ssashton/cyrus-pre-volume/Cyrus Pre Audio Measurments/Cyrus Pre Volume Original.png

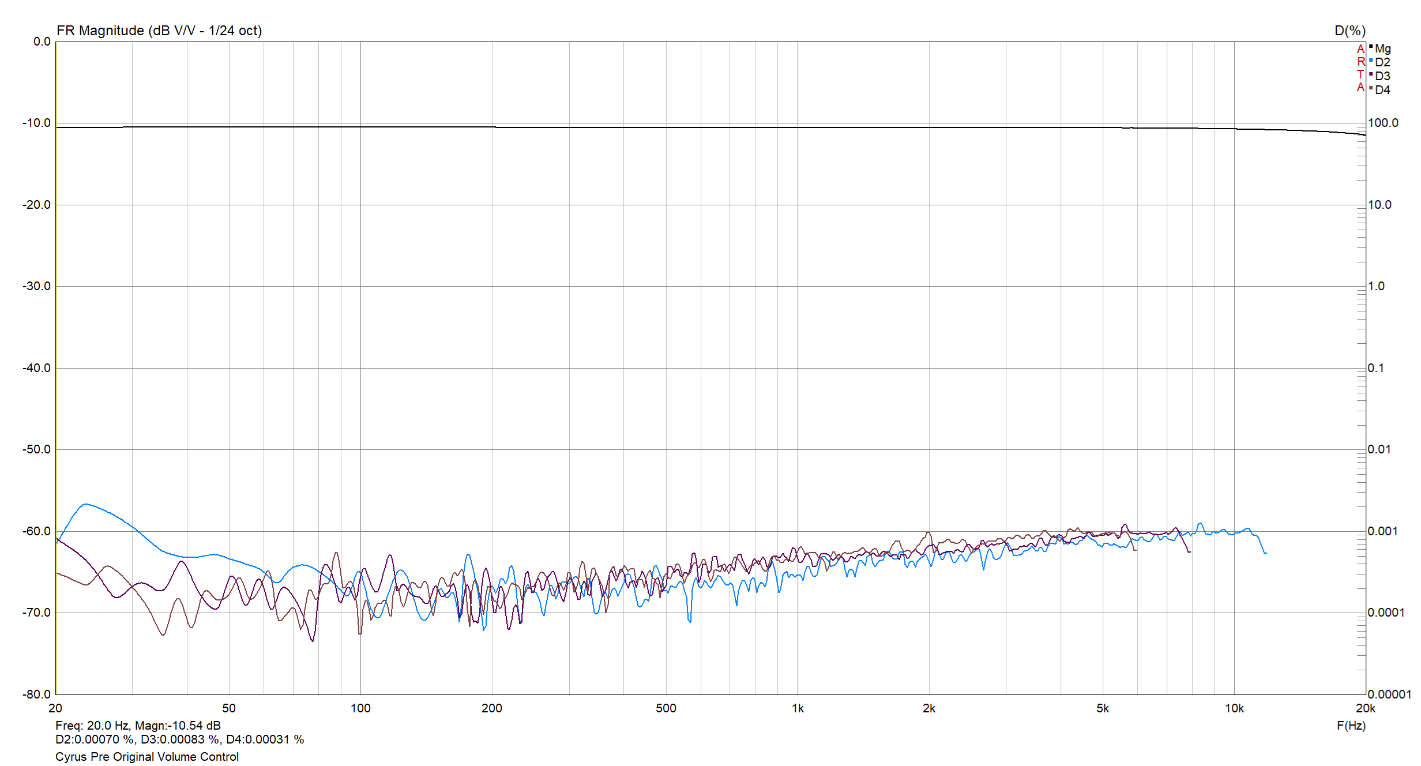
Cyrus Pre Audio Measurments/Cyrus Pre Volume Original.png
