ssashton/cyrus-pre-volume/Cyrus Pre Images/0fe24d15-2bc2-4b44-9fb7-35bb59eaa051.jpg

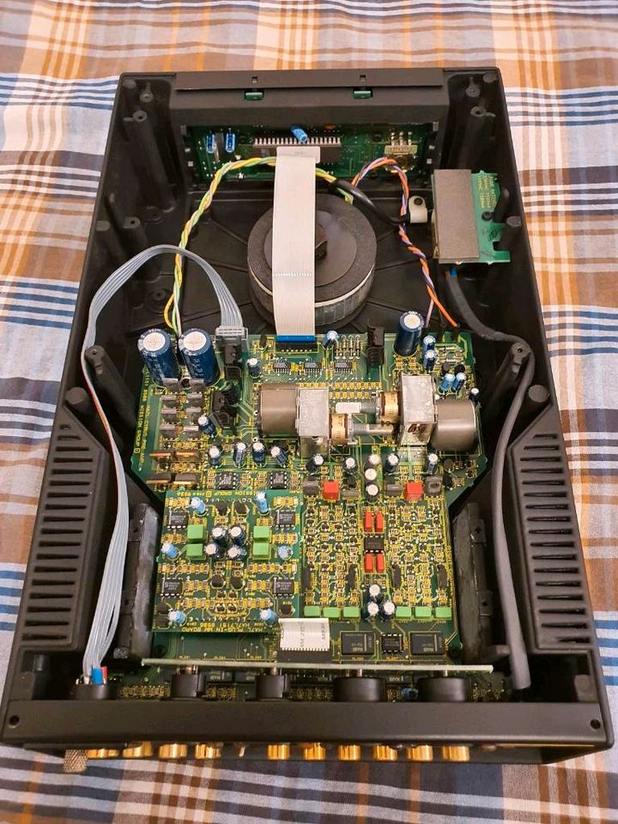
Cyrus Pre Images/0fe24d15-2bc2-4b44-9fb7-35bb59eaa051.jpg
