ssashton/cyrus-pre-volume/Cyrus Pre Images/20250813_225020.jpg

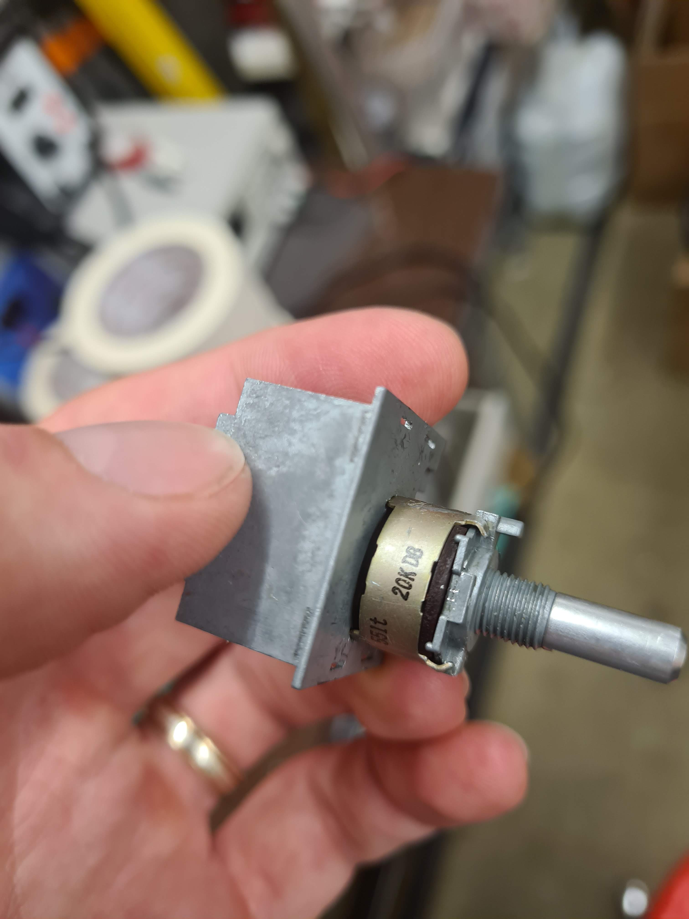
Cyrus Pre Images/20250813_225020.jpg
