ssashton/cyrus-pre-volume/Cyrus Pre Images/20250813_225022.jpg

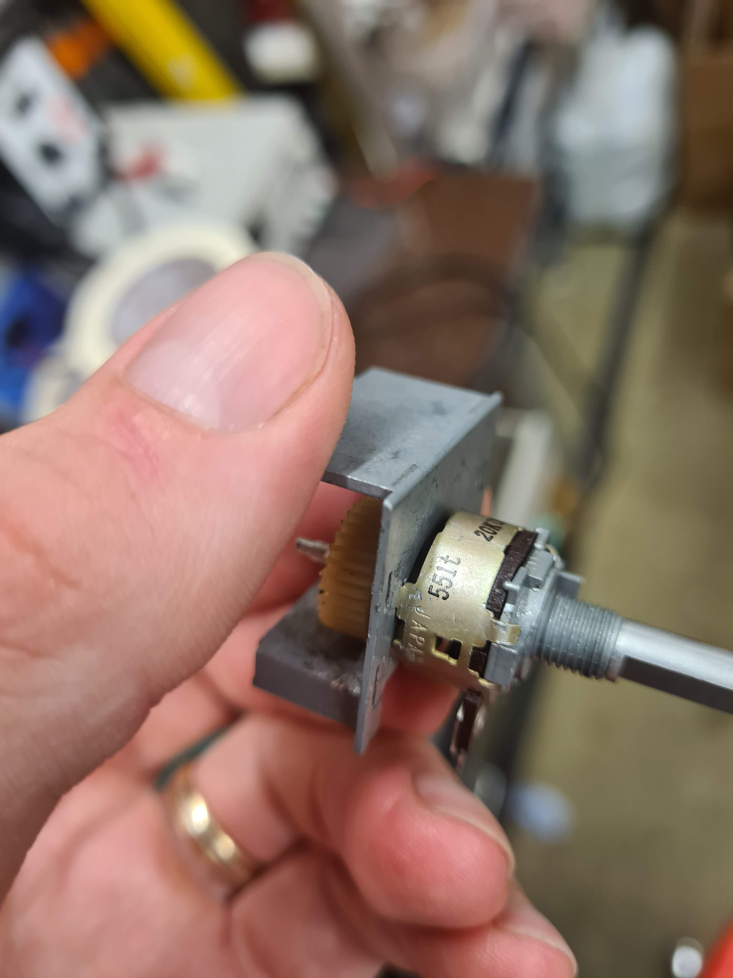
Cyrus Pre Images/20250813_225022.jpg
