ssashton/cyrus-pre-volume/Cyrus Pre Images/20251005_141955.jpg

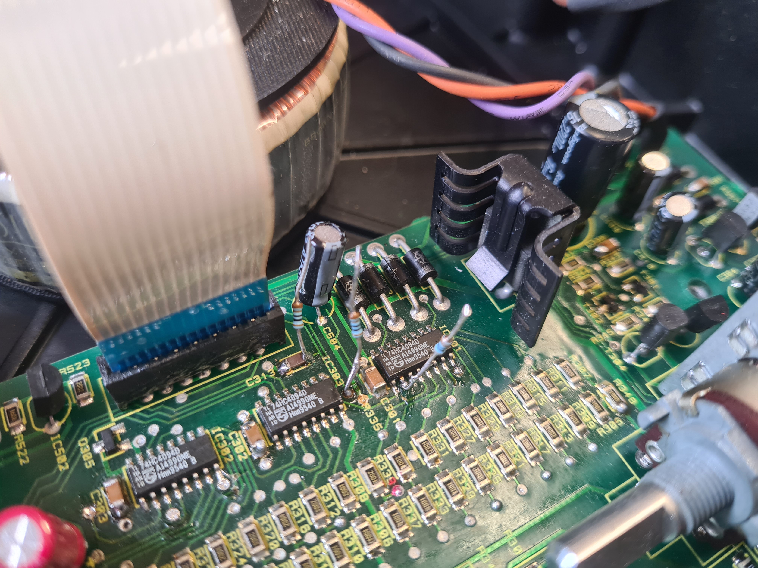
Cyrus Pre Images/20251005_141955.jpg
