ssashton/cyrus-pre-volume/Cyrus Pre Images/20251005_143241.jpg

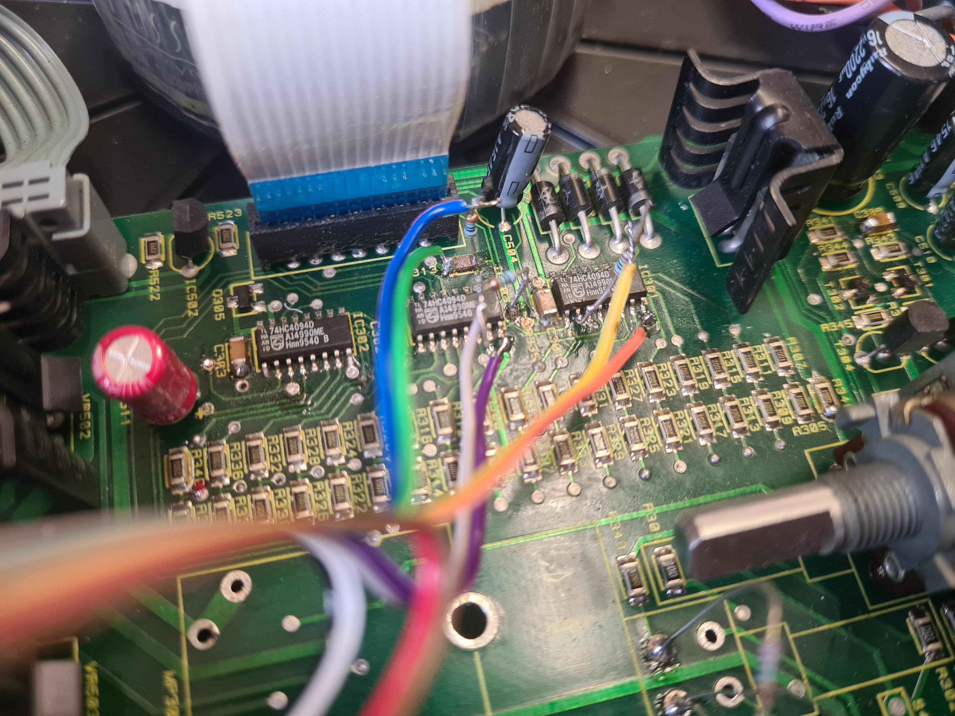
Cyrus Pre Images/20251005_143241.jpg
