ssashton/cyrus-pre-volume/Cyrus Pre Images/20251005_143256.jpg

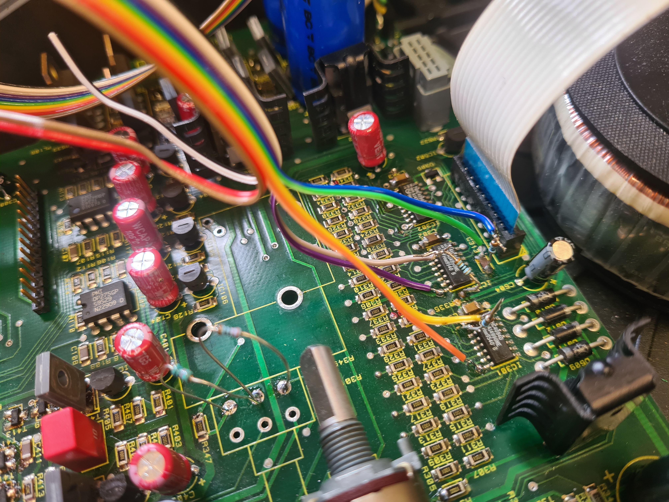
Cyrus Pre Images/20251005_143256.jpg
