ssashton/cyrus-pre-volume/Cyrus Pre Images/20251109_150557.jpg

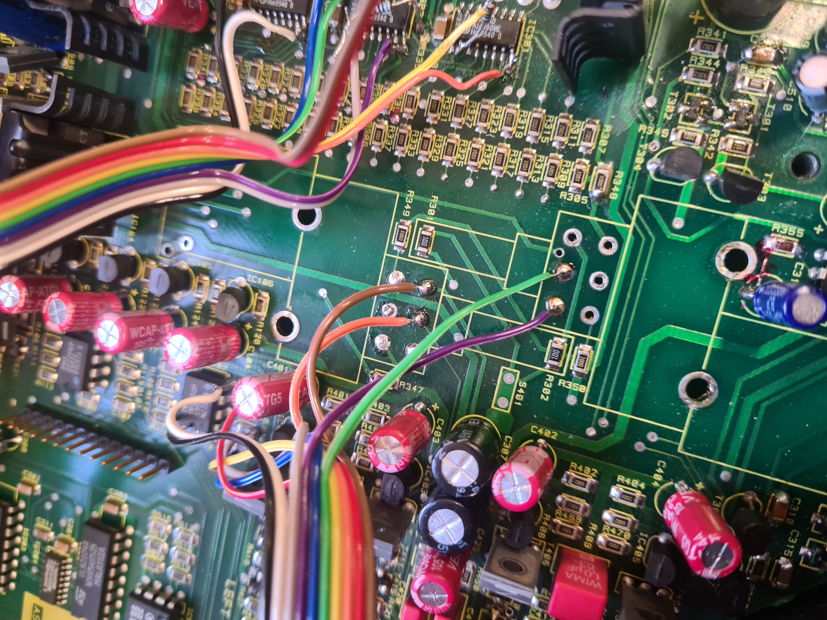
Cyrus Pre Images/20251109_150557.jpg
