ssashton/cyrus-pre-volume/Cyrus Pre Images/20251109_150601.jpg

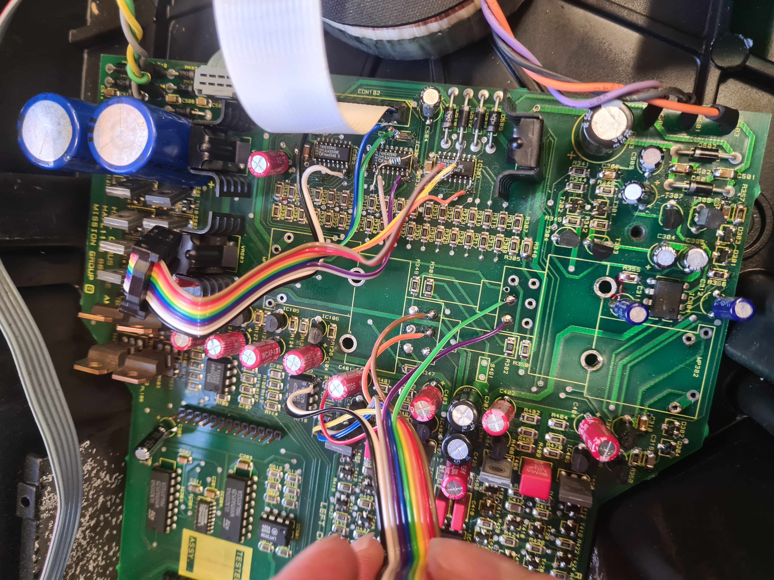
Cyrus Pre Images/20251109_150601.jpg
