ssashton/cyrus-pre-volume/Cyrus Pre Images/20251109_150613.jpg

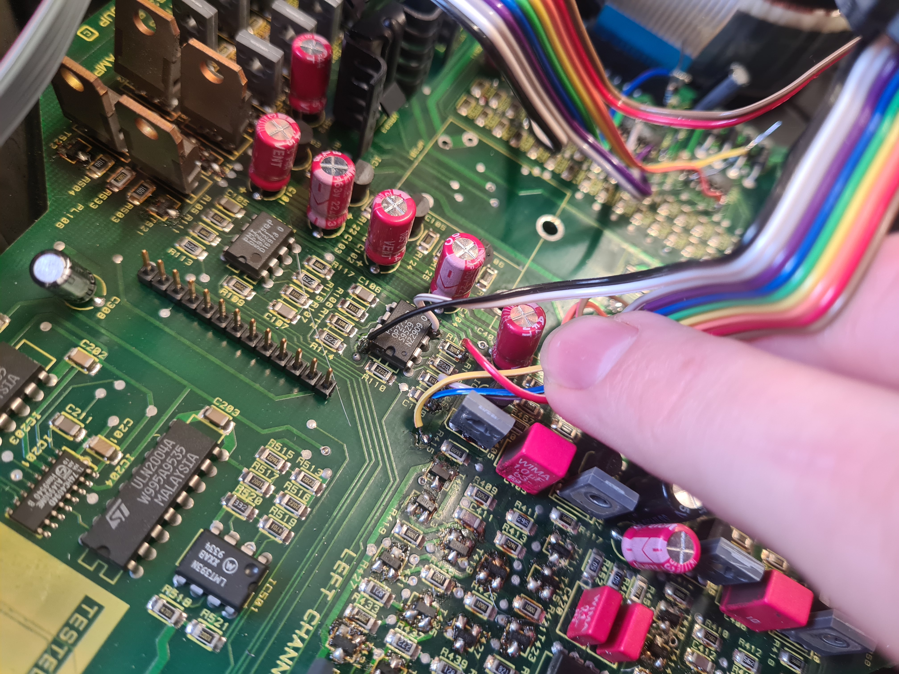
Cyrus Pre Images/20251109_150613.jpg
