ssashton/cyrus-pre-volume/Cyrus Pre Images/c8a0d77d-515b-400d-b8cd-d2a9fd72f0e5.jpg

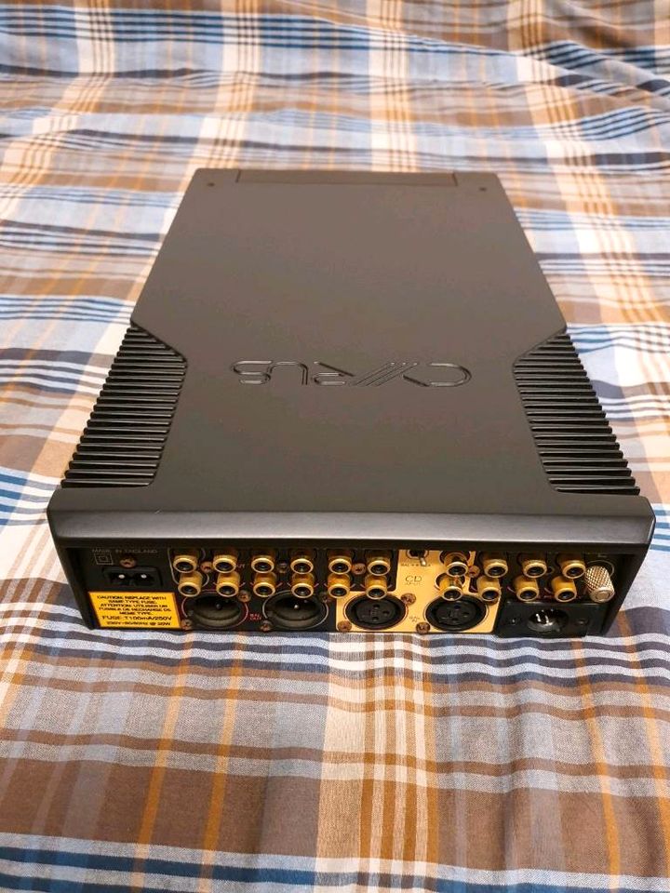
Cyrus Pre Images/c8a0d77d-515b-400d-b8cd-d2a9fd72f0e5.jpg
