ssashton/cyrus-pre-volume/Cyrus Pre Images/mission_pre_pot.jpg

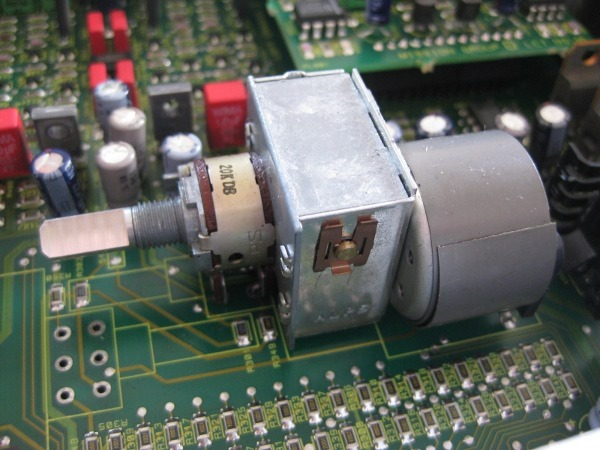
Cyrus Pre Images/mission_pre_pot.jpg
