ssashton/cyrus-pre-volume/Cyrus Pre Images/20251005_141931.jpg

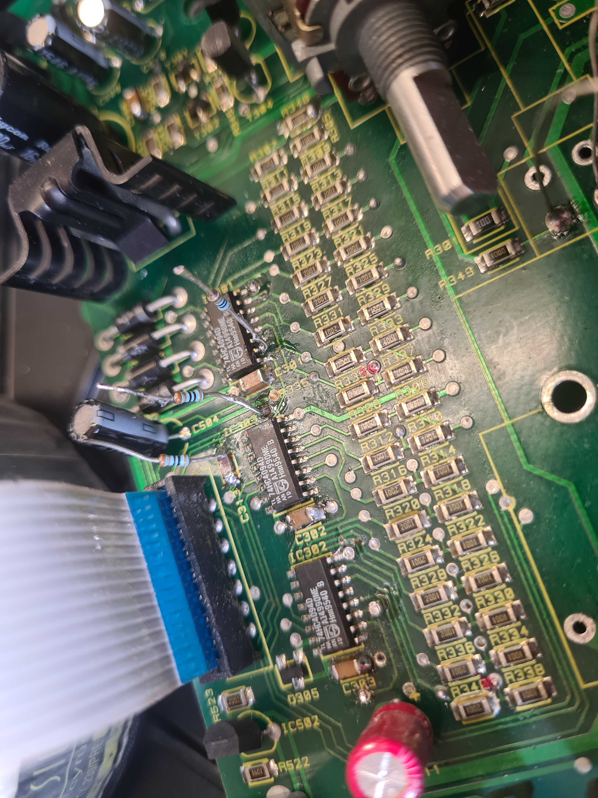
Cyrus Pre Images/20251005_141931.jpg
