ssashton/cyrus-pre-volume/Cyrus Pre Images/20251006_142524.jpg

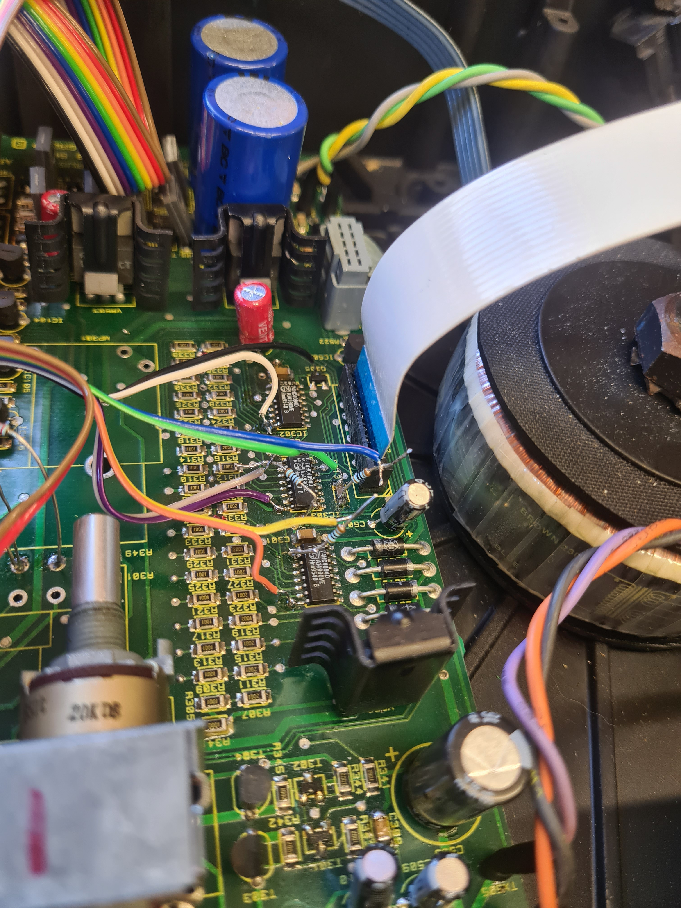
Cyrus Pre Images/20251006_142524.jpg
