ssashton/cyrus-pre-volume/Cyrus Pre Images/20251109_151317.jpg

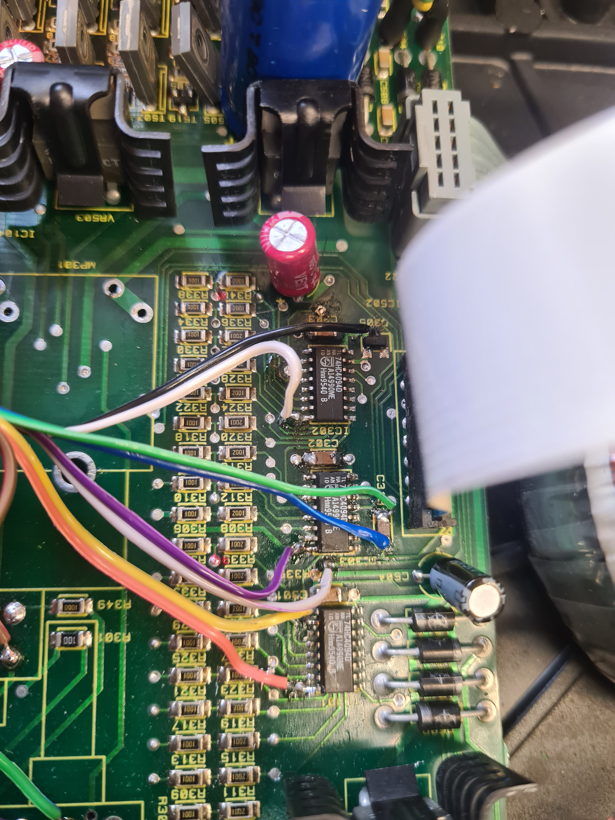
Cyrus Pre Images/20251109_151317.jpg
