ssashton/cyrus-pre-volume/Cyrus Pre Images/20251109_151350.jpg

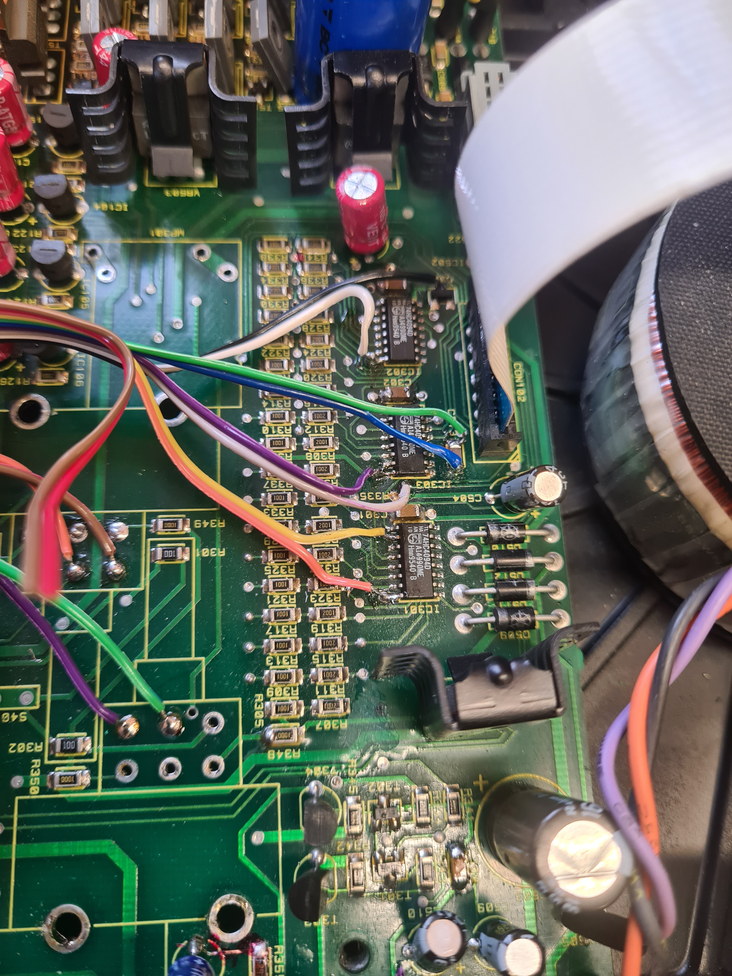
Cyrus Pre Images/20251109_151350.jpg
