ssashton/cyrus-pre-volume/Cyrus Pre Images/20251109_151352.jpg

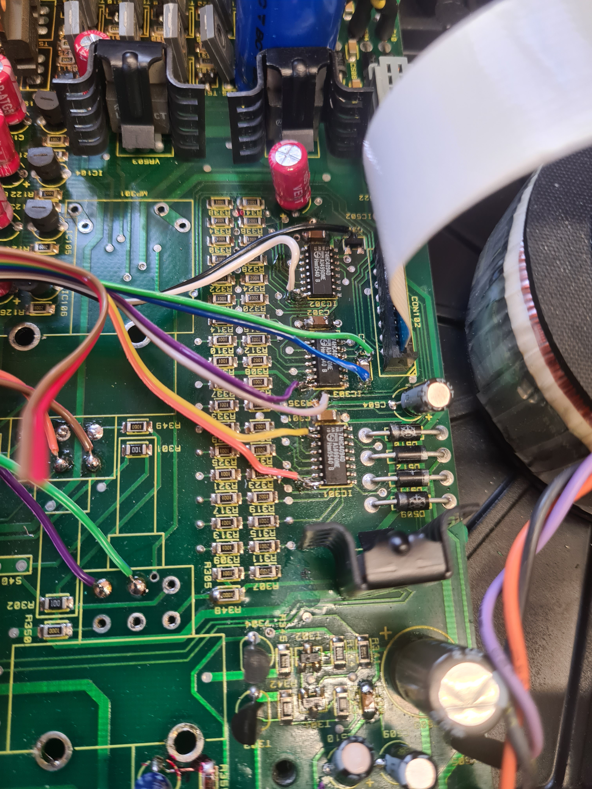
Cyrus Pre Images/20251109_151352.jpg
