ssashton/cyrus-pre-volume/Cyrus Pre Images/20251109_152031.jpg

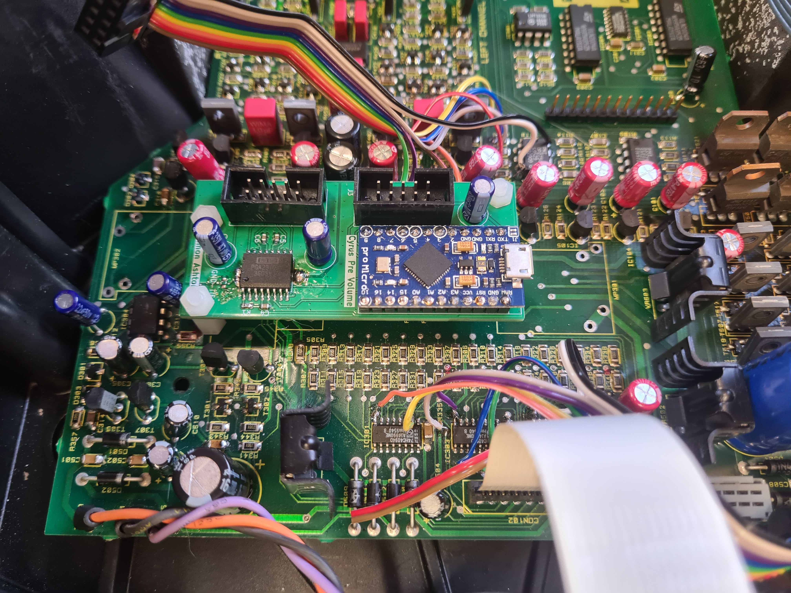
Cyrus Pre Images/20251109_152031.jpg
