ssashton/cyrus-pre-volume/Cyrus Pre Images/20251109_153733.jpg

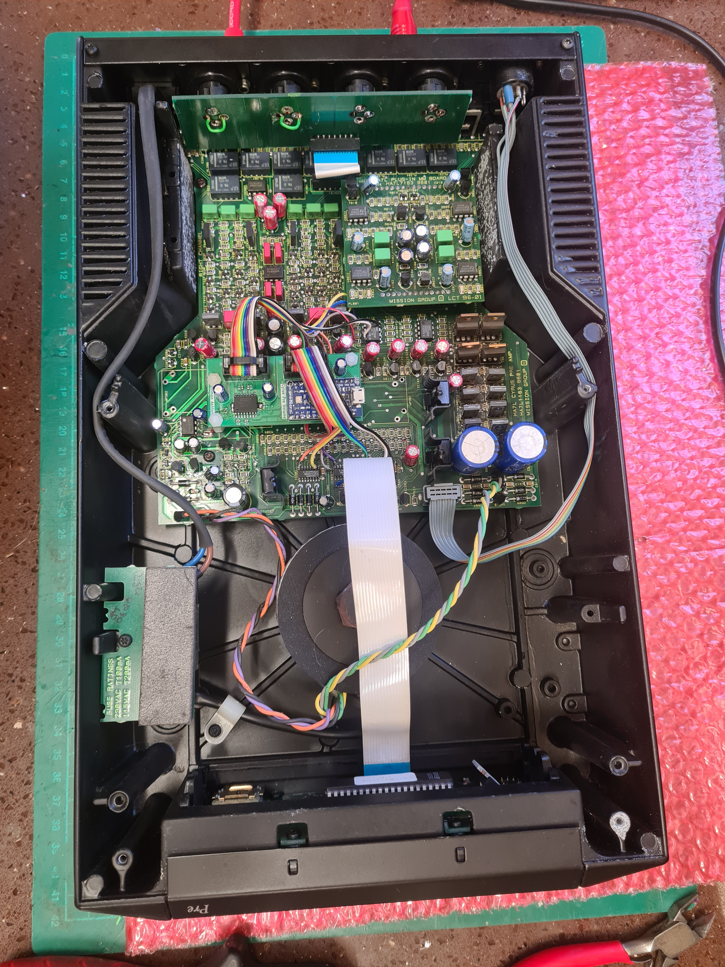
Cyrus Pre Images/20251109_153733.jpg
